Muny/DIY-JBC-T245-Station/arduino_t245_controller/futuramdcn12pt7b.h

const uint8_t futura_medium_condensed_bt12pt7bBitmaps[] PROGMEM = {
  0x6D, 0xB6, 0xDB, 0x6D, 0xB0, 0x3F, 0xE0, 0x99, 0x99, 0x99, 0x00, 0xCC,
  0x01, 0x8C, 0x01, 0x8C, 0x01, 0x08, 0x03, 0x18, 0x03, 0x18, 0x3F, 0xFF,
  0x46, 0x30, 0x06, 0x20, 0x0C, 0x60, 0xFF, 0xFE, 0x08, 0xC0, 0x18, 0xC0,
  0x18, 0x80, 0x11, 0x80, 0x31, 0x80, 0x31, 0x00, 0x28, 0x28, 0x7C, 0x7E,
  0xE3, 0xC0, 0xC0, 0xC0, 0xE0, 0x78, 0x1C, 0x0E, 0x07, 0x03, 0x03, 0x43,
  0xC7, 0xFE, 0x7C, 0x28, 0x28, 0x78, 0x18, 0xFC, 0x30, 0xCC, 0x20, 0xCC,
  0x60, 0xCC, 0x60, 0xCC, 0x40, 0xCC, 0xC0, 0xCC, 0x9E, 0xFD, 0xBF, 0x79,
  0x33, 0x03, 0x33, 0x02, 0x33, 0x06, 0x33, 0x06, 0x33, 0x04, 0x33, 0x0C,
  0x3F, 0x18, 0x1E, 0x1C, 0x07, 0xC1, 0x8C, 0x31, 0x86, 0x30, 0xCC, 0x0F,
  0x81, 0xE0, 0x38, 0x0F, 0x83, 0xB9, 0x63, 0x7C, 0x7D, 0x87, 0x39, 0xE3,
  0xFE, 0x3C, 0xE0, 0xFC, 0x33, 0x66, 0x66, 0xCC, 0xCC, 0xCC, 0xCC, 0xCC,
  0xC6, 0x66, 0x63, 0x30, 0xCC, 0x66, 0x66, 0x33, 0x33, 0x33, 0x33, 0x33,
  0x36, 0x66, 0x6C, 0xC0, 0x11, 0x25, 0xF1, 0xCF, 0xD2, 0x44, 0x00, 0x02,
  0x00, 0x10, 0x00, 0x80, 0x04, 0x00, 0x20, 0x01, 0x03, 0xFF, 0xE0, 0x40,
  0x02, 0x00, 0x10, 0x00, 0x80, 0x04, 0x00, 0x20, 0x00, 0x6D, 0x2D, 0x00,
  0xFF, 0xC0, 0xFF, 0x80, 0x06, 0x0C, 0x10, 0x60, 0xC1, 0x86, 0x0C, 0x18,
  0x20, 0xC1, 0x83, 0x0C, 0x18, 0x30, 0x41, 0x83, 0x00, 0x3C, 0x7E, 0x66,
  0xC3, 0xC3, 0xC3, 0xC3, 0xC3, 0xC3, 0xC3, 0xC3, 0xC3, 0xC3, 0xC3, 0x67,
  0x7E, 0x3C, 0xFF, 0x33, 0x33, 0x33, 0x33, 0x33, 0x33, 0x33, 0x30, 0x3C,
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
  {   586,  10,  17,  12,    1,  -16 },   // 0x47 'G'
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

const GFXfont futura_medium_condensed_bt12pt7b PROGMEM = {
  (uint8_t  *)futura_medium_condensed_bt12pt7bBitmaps,
  (GFXglyph *)futura_medium_condensed_bt12pt7bGlyphs,
  0x20, 0x7E, 28 };

// Approx. 2033 bytes
