Muny/DIY-JBC-T245-Station/arduino_t245_controller/futuramdcn22pt7b.h

const uint8_t futura_medium_condensed_bt22pt7bBitmaps[] PROGMEM = {
  0x7B, 0xDE, 0xF7, 0xBD, 0xEF, 0x7B, 0xDE, 0xF7, 0xBD, 0xEF, 0x7B, 0xDE,
  0xF7, 0xBD, 0xE0, 0x00, 0x1D, 0xFF, 0xFD, 0xC0, 0xC7, 0x8F, 0x1E, 0x3C,
  0x78, 0xF1, 0xE3, 0xC7, 0x8F, 0x1E, 0x30, 0x00, 0x03, 0x81, 0xC0, 0x00,
  0x1C, 0x1C, 0x00, 0x01, 0xC0, 0xE0, 0x00, 0x0E, 0x07, 0x00, 0x00, 0x70,
  0x70, 0x00, 0x07, 0x03, 0x80, 0x00, 0x38, 0x1C, 0x00, 0x01, 0xC1, 0xC0,
  0x00, 0x1C, 0x0E, 0x00, 0x00, 0xE0, 0x70, 0x07, 0xFF, 0xFF, 0xFE, 0x3F,
  0xFF, 0xFF, 0xF1, 0xFF, 0xFF, 0xFF, 0x10, 0x1C, 0x1C, 0x00, 0x01, 0xC0,
  0xE0, 0x00, 0x0E, 0x07, 0x00, 0x00, 0x70, 0x70, 0x00, 0x07, 0x03, 0x80,
  0x00, 0x38, 0x1C, 0x00, 0xFF, 0xFF, 0xFF, 0xCF, 0xFF, 0xFF, 0xFC, 0x7F,
  0xFF, 0xFF, 0xE0, 0x07, 0x07, 0x00, 0x00, 0x70, 0x38, 0x00, 0x03, 0x81,
  0xC0, 0x00, 0x38, 0x1C, 0x00, 0x01, 0xC0, 0xE0, 0x00, 0x0E, 0x0E, 0x00,
  0x00, 0xE0, 0x70, 0x00, 0x07, 0x03, 0x80, 0x00, 0x78, 0x38, 0x00, 0x00,
  0x0C, 0xC0, 0x33, 0x00, 0xCC, 0x03, 0x30, 0x0F, 0xC0, 0xFF, 0xC7, 0xFF,
  0x9F, 0xFE, 0xFC, 0x7F, 0xE0, 0xCF, 0x00, 0x3C, 0x00, 0xF0, 0x03, 0xC0,
  0x0F, 0x80, 0x3E, 0x00, 0x7E, 0x01, 0xFC, 0x03, 0xF8, 0x03, 0xF8, 0x07,
  0xF0, 0x07, 0xE0, 0x0F, 0x80, 0x1F, 0x00, 0x7C, 0x00, 0xF0, 0x03, 0xC0,
  0x0F, 0x00, 0x3C, 0x80, 0xF7, 0x07, 0xFE, 0x3E, 0x7F, 0xF9, 0xFF, 0xC3,
  0xFE, 0x03, 0xF0, 0x0C, 0xC0, 0x33, 0x00, 0xCC, 0x03, 0x30, 0x1F, 0x00,
  0x0E, 0x01, 0xFE, 0x00, 0x38, 0x07, 0xFC, 0x01, 0xC0, 0x1C, 0x70, 0x07,
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
  {  1966,  18,  32,  21,    2,  -31 },   // 0x47 'G'
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

const GFXfont futura_medium_condensed_bt22pt7b PROGMEM = {
  (uint8_t  *)futura_medium_condensed_bt22pt7bBitmaps,
  (GFXglyph *)futura_medium_condensed_bt22pt7bGlyphs,
  0x20, 0x7E, 52 };

// Approx. 5249 bytes
