Muny/DIY-JBC-T245-Station/arduino_t245_controller/futuramdcn23pt7b.h

const uint8_t futura_medium_condensed_bt23pt7bBitmaps[] PROGMEM = {
  0x7B, 0xDE, 0xF7, 0xBD, 0xEF, 0x7B, 0xDE, 0xF7, 0xBD, 0xEF, 0x7B, 0xDE,
  0xF7, 0xBD, 0xEF, 0x00, 0x00, 0xEF, 0xFF, 0xEE, 0xE1, 0xF8, 0x7E, 0x1F,
  0x87, 0xE1, 0xF8, 0x7E, 0x1F, 0x87, 0xE1, 0xF8, 0x7E, 0x1F, 0x87, 0x00,
  0x01, 0xC0, 0xE0, 0x00, 0x0E, 0x07, 0x00, 0x00, 0x38, 0x1C, 0x00, 0x01,
  0xE0, 0xF0, 0x00, 0x07, 0x03, 0x80, 0x00, 0x1C, 0x0E, 0x00, 0x00, 0xF0,
  0x78, 0x00, 0x03, 0x81, 0xC0, 0x00, 0x0E, 0x07, 0x00, 0x00, 0x78, 0x38,
  0x01, 0xFF, 0xFF, 0xFF, 0xC7, 0xFF, 0xFF, 0xFF, 0x1F, 0xFF, 0xFF, 0xF8,
  0x00, 0xE0, 0x70, 0x00, 0x03, 0x81, 0xC0, 0x00, 0x1C, 0x0E, 0x00, 0x00,
  0x70, 0x38, 0x00, 0x03, 0xC1, 0xE0, 0x00, 0x0E, 0x07, 0x00, 0x1F, 0xFF,
  0xFF, 0xF8, 0xFF, 0xFF, 0xFF, 0xE3, 0xFF, 0xFF, 0xFF, 0x80, 0x1C, 0x0E,
  0x00, 0x00, 0xF0, 0x78, 0x00, 0x03, 0x81, 0xC0, 0x00, 0x0E, 0x07, 0x00,
  0x00, 0x78, 0x3C, 0x00, 0x01, 0xC0, 0xE0, 0x00, 0x07, 0x03, 0x80, 0x00,
  0x38, 0x1C, 0x00, 0x00, 0xE0, 0x70, 0x00, 0x07, 0x83, 0xC0, 0x00, 0x06,
  0x60, 0x0C, 0xC0, 0x19, 0x80, 0x33, 0x00, 0x7F, 0x03, 0xFF, 0x0F, 0xFF,
  0x3F, 0xFE, 0x7C, 0x3F, 0xF0, 0x3B, 0xC0, 0x67, 0x80, 0x0F, 0x00, 0x1E,
  0x00, 0x3C, 0x00, 0x7C, 0x00, 0x7C, 0x00, 0xFE, 0x00, 0xFE, 0x00, 0xFE,
  0x00, 0xFF, 0x00, 0x7F, 0x00, 0x3F, 0x00, 0x3E, 0x00, 0x3E, 0x00, 0x7C,
  0x00, 0x78, 0x00, 0xF0, 0x01, 0xE0, 0x03, 0xC4, 0x07, 0xB8, 0x1F, 0xF8,
  0x7C, 0xFF, 0xF9, 0xFF, 0xE0, 0xFF, 0x80, 0x7E, 0x00, 0xCC, 0x01, 0x98,
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
  {  2124,  19,  33,  22,    2,  -32 },   // 0x47 'G'
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

const GFXfont futura_medium_condensed_bt23pt7b PROGMEM = {
  (uint8_t  *)futura_medium_condensed_bt23pt7bBitmaps,
  (GFXglyph *)futura_medium_condensed_bt23pt7bGlyphs,
  0x20, 0x7E, 54 };

// Approx. 5608 bytes
