Muny/DIY-JBC-T245-Station/arduino_t245_controller/futuramdcn24pt7b.h

const uint8_t futura_medium_condensed_bt24pt7bBitmaps[] PROGMEM = {
  0xF7, 0xBD, 0xEF, 0x7B, 0xDE, 0xF7, 0xBD, 0xEF, 0x7B, 0xDE, 0xF7, 0xBD,
  0xEF, 0x7B, 0xDE, 0xF7, 0x80, 0x00, 0x3B, 0xFF, 0xFB, 0x80, 0xE1, 0xF8,
  0x7E, 0x1F, 0x87, 0xE1, 0xF8, 0x7E, 0x1F, 0x87, 0xE1, 0xF8, 0x7E, 0x1F,
  0x87, 0xE1, 0xC0, 0x00, 0x01, 0xE0, 0xF0, 0x00, 0x03, 0x81, 0xC0, 0x00,
  0x0F, 0x03, 0x80, 0x00, 0x1C, 0x0E, 0x00, 0x00, 0x38, 0x1C, 0x00, 0x00,
  0xF0, 0x78, 0x00, 0x01, 0xC0, 0xE0, 0x00, 0x07, 0x81, 0xC0, 0x00, 0x0E,
  0x07, 0x80, 0x00, 0x1C, 0x0E, 0x00, 0x7F, 0xFF, 0xFF, 0xF8, 0xFF, 0xFF,
  0xFF, 0xF1, 0xFF, 0xFF, 0xFF, 0xC0, 0x07, 0x81, 0xC0, 0x00, 0x0E, 0x07,
  0x00, 0x00, 0x1C, 0x0E, 0x00, 0x00, 0x70, 0x3C, 0x00, 0x00, 0xE0, 0x70,
  0x00, 0x03, 0xC0, 0xE0, 0x03, 0xFF, 0xFF, 0xFF, 0x8F, 0xFF, 0xFF, 0xFF,
  0x1F, 0xFF, 0xFF, 0xFE, 0x00, 0x70, 0x3C, 0x00, 0x00, 0xE0, 0x70, 0x00,
  0x03, 0xC0, 0xE0, 0x00, 0x07, 0x03, 0xC0, 0x00, 0x0E, 0x07, 0x00, 0x00,
  0x3C, 0x0E, 0x00, 0x00, 0x70, 0x3C, 0x00, 0x00, 0xE0, 0x70, 0x00, 0x03,
  0xC0, 0xE0, 0x00, 0x07, 0x03, 0xC0, 0x00, 0x1E, 0x07, 0x00, 0x00, 0x06,
  0x60, 0x06, 0x60, 0x06, 0x60, 0x06, 0x60, 0x07, 0xF0, 0x1F, 0xF8, 0x3F,
  0xFC, 0x7F, 0xFE, 0x7E, 0x3F, 0xFC, 0x1E, 0xF8, 0x08, 0xF8, 0x00, 0xF8,
  0x00, 0xF8, 0x00, 0xF8, 0x00, 0xF8, 0x00, 0xFC, 0x00, 0x7E, 0x00, 0x7F,
  0x00, 0x3F, 0xC0, 0x1F, 0xE0, 0x0F, 0xF0, 0x03, 0xFC, 0x01, 0xFC, 0x00,
  0xFE, 0x00, 0x7E, 0x00, 0x3F, 0x00, 0x1F, 0x00, 0x1F, 0x00, 0x1F, 0x00,
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
  {  2348,  20,  35,  23,    2,  -34 },   // 0x47 'G'
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

const GFXfont futura_medium_condensed_bt24pt7b PROGMEM = {
  (uint8_t  *)futura_medium_condensed_bt24pt7bBitmaps,
  (GFXglyph *)futura_medium_condensed_bt24pt7bGlyphs,
  0x20, 0x7E, 56 };

// Approx. 6126 bytes
