Muny/DIY-JBC-T245-Station/arduino_t245_controller/futuramdcn9pt7b.h

const uint8_t futura_medium_condensed_bt9pt7bBitmaps[] PROGMEM = {
  0xFF, 0xFF, 0xF3, 0xC0, 0xB6, 0xDA, 0x02, 0x60, 0x64, 0x04, 0x40, 0x4C,
  0x04, 0x87, 0xFF, 0x09, 0x81, 0x90, 0xFF, 0xE1, 0x20, 0x32, 0x02, 0x60,
  0x64, 0x00, 0x28, 0xA7, 0xBF, 0xCF, 0x0C, 0x1C, 0x38, 0x70, 0xC3, 0xCF,
  0xF7, 0x8A, 0x28, 0x60, 0xC9, 0x08, 0x91, 0x09, 0x10, 0x92, 0x09, 0x20,
  0x64, 0x60, 0x49, 0x04, 0x90, 0x89, 0x08, 0x91, 0x09, 0x30, 0x60, 0x38,
  0x6C, 0x6C, 0x6C, 0x68, 0x38, 0x30, 0x70, 0xDB, 0xCE, 0xCE, 0xFE, 0x73,
  0xF8, 0x2D, 0xAD, 0xB6, 0xDB, 0x6C, 0x9B, 0x20, 0x9B, 0x26, 0xDB, 0x6D,
  0xB6, 0xB6, 0x80, 0x25, 0x5D, 0xF2, 0x00, 0x04, 0x00, 0x80, 0x10, 0x02,
  0x00, 0x41, 0xFF, 0xC1, 0x00, 0x20, 0x04, 0x00, 0x80, 0x10, 0x00, 0x5A,
  0x80, 0xF0, 0xF0, 0x08, 0xC4, 0x21, 0x18, 0x84, 0x62, 0x10, 0x8C, 0x40,
  0x79, 0xEC, 0xF3, 0xCF, 0x3C, 0xF3, 0xCF, 0x3C, 0xDE, 0x78, 0xFF, 0x33,
  0x33, 0x33, 0x33, 0x33, 0x30, 0x7B, 0xFC, 0xF3, 0x0C, 0x61, 0x8C, 0x30,
  0x86, 0x1F, 0xFC, 0x7B, 0xFC, 0xF3, 0x0C, 0xE3, 0x83, 0x0C, 0x3C, 0xFF,
  0x78, 0x18, 0x63, 0x8E, 0x59, 0x69, 0xBF, 0xFC, 0x61, 0x86, 0x18, 0x3C,
  0xF6, 0x18, 0x41, 0xE7, 0xC3, 0x0C, 0x31, 0xFE, 0xF0, 0x18, 0xC3, 0x18,
  0x63, 0x6F, 0xF3, 0xCF, 0x3C, 0xFF, 0x78, 0xFF, 0xF0, 0x86, 0x18, 0x43,
  0x0C, 0x21, 0x86, 0x10, 0xC0, 0x7B, 0xFC, 0xF3, 0xCD, 0xE7, 0xB3, 0xCF,
  0x3C, 0xFF, 0x78, 0x7B, 0xEC, 0xF3, 0xCF, 0x3F, 0xDB, 0x18, 0x63, 0x0C,
  0x60, 0xF0, 0xF0, 0xF0, 0x7A, 0x80, 0x00, 0x40, 0xE0, 0xC1, 0xC0, 0xC0,
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
  {   352,   7,  13,   9,    1,  -12 },   // 0x47 'G'
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

const GFXfont futura_medium_condensed_bt9pt7b PROGMEM = {
  (uint8_t  *)futura_medium_condensed_bt9pt7bBitmaps,
  (GFXglyph *)futura_medium_condensed_bt9pt7bGlyphs,
  0x20, 0x7E, 21 };

// Approx. 1457 bytes
